TomasSpusta/CFNano_BlueBox/SOFTWARE/model_classes.py

from dataclasses import dataclass


@dataclass
class User:
    id: str = ""
    name: str = ""
    full_name: str = ""
    card_id: str = ""


@dataclass
class Instrument:
    id: str = ""
    name: str = ""
    mac_address: str = ""
    ip: str = ""


@dataclass
class Reservation:
    remaining_time: int = 0
    recording_id: str = ""
    reservation_id: str = ""
    warning_sent: bool = False
    ended_by_user: bool = False
    ended_by_time: bool = False


@dataclass
class Token:
    string: str
    expiration: str

    def to_dict(self):
        return {"string": self.string, "expiration": self.expiration}
